t-dsp/t-dsp_tac5212_audio_shield_adaptor/3d_models/PinHeader_1x02_P2.54mm_Vertical.step

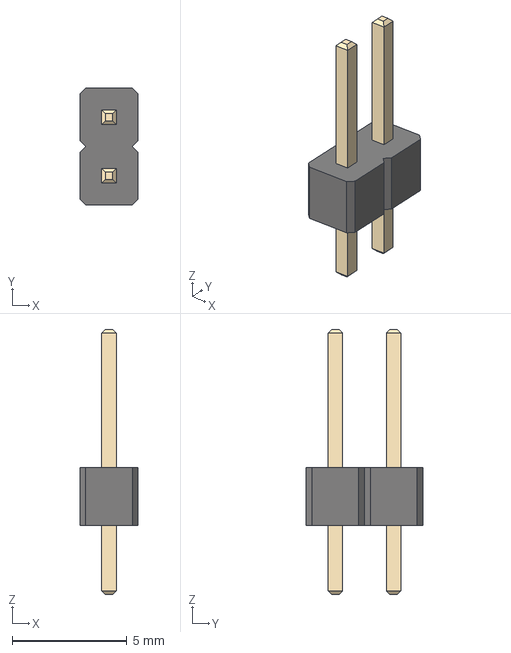
[picture p15: CAD file, 2026-03-01]
3d_models/PinHeader_1x02_P2.54mm_Vertical.step
2.54 x 5.08 x 11.5 mm
