t-dsp/t-dsp_tac5212_audio_shield_adaptor/3d_models/74LS00.step

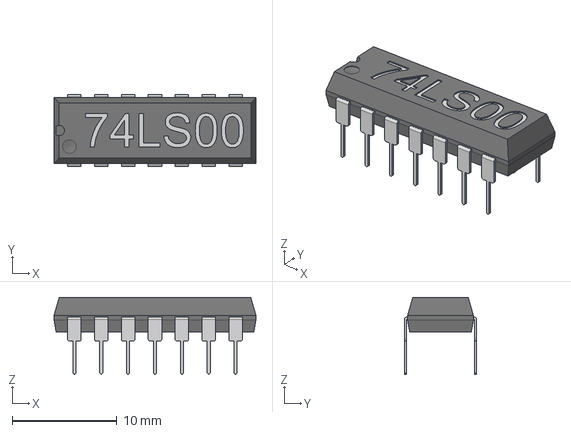
[picture p16: CAD file, 2026-03-01]
3d_models/74LS00.step
19.3 x 6.90 x 7.40 mm
