t-dsp/t-dsp_tac5212_audio_shield_adaptor/3d_models/d-nc3fah.stp

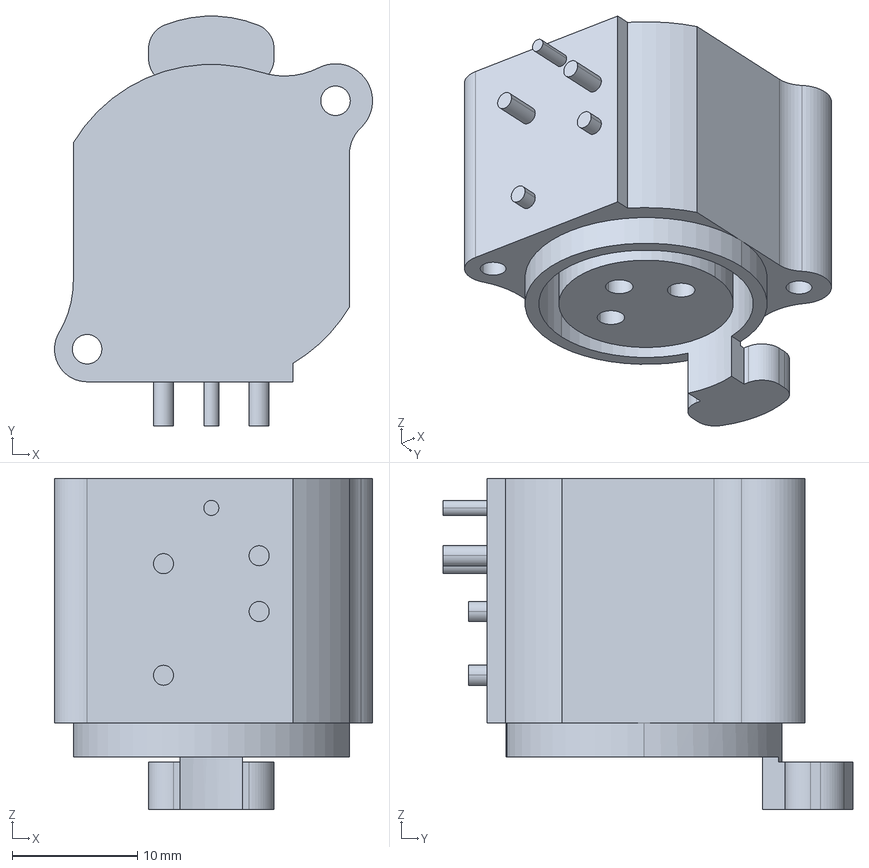
[picture p17: CAD file, 2026-03-01]
3d_models/d-nc3fah.stp
25.3 x 32.6 x 26.4 mm
