t-dsp/t-dsp_tac5212_audio_shield_adaptor/3d_models/COMBO_XLR_NCJ6FI-H-0.stp

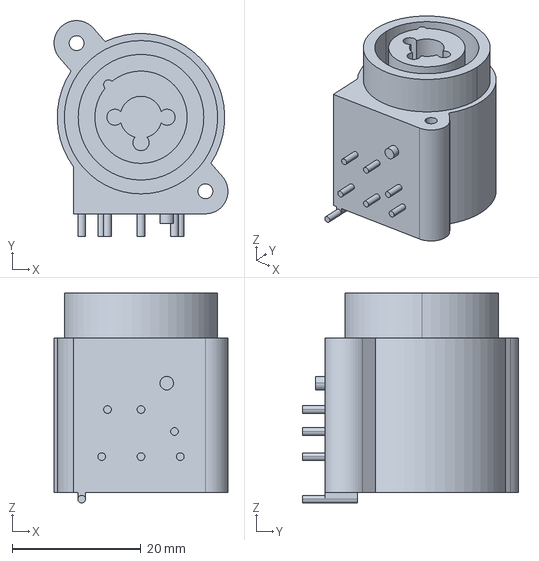
[picture p18: CAD file, 2026-03-01]
3d_models/COMBO_XLR_NCJ6FI-H-0.stp
27.0 x 33.5 x 32.6 mm
