t-dsp/t-dsp_tac5212_audio_shield_adaptor/3d_models/COMBO-NCJ6FA-H.step

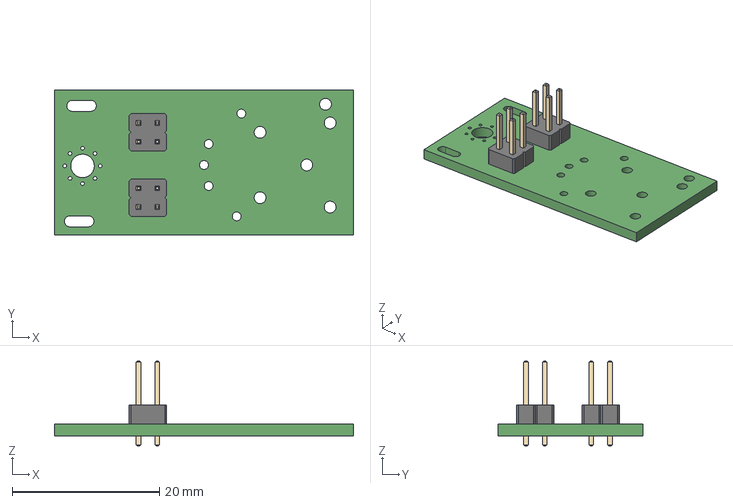
[picture p19: CAD file, 2026-03-01]
3d_models/COMBO-NCJ6FA-H.step
40.6 x 19.7 x 11.5 mm
