t-dsp/t-dsp_tac5212_audio_shield_adaptor/3d_models/35RAPC7JS_SIMPLIFIED.step

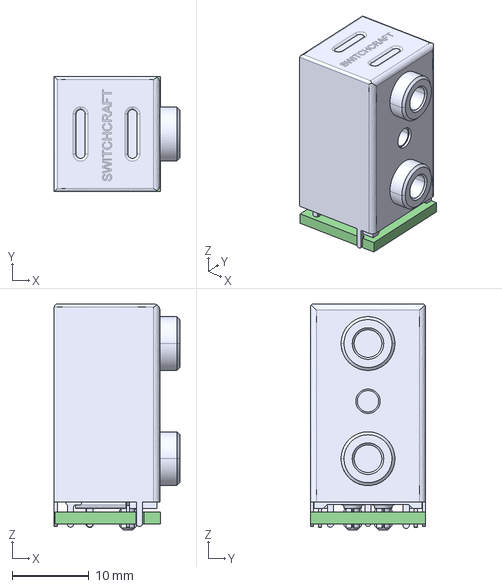
[picture p21: CAD file, 2026-03-01]
3d_models/35RAPC7JS_SIMPLIFIED.step
16.4 x 15.0 x 29.5 mm
IO_3.5_35RAPC7JS PCB
