t-dsp/t-dsp_tac5212_audio_shield_adaptor/3d_models/TFT_320x240_touch_r0.step

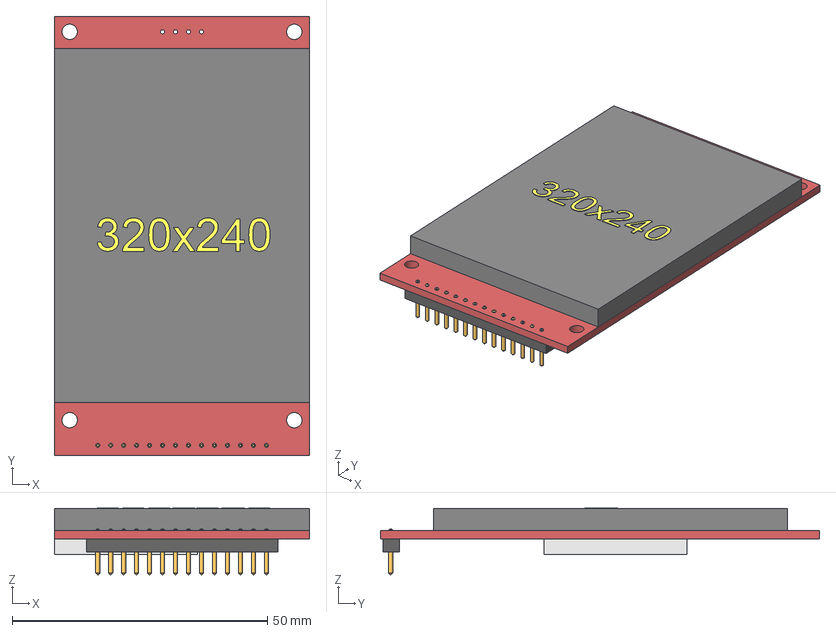
[picture p22: CAD file, 2026-03-01]
3d_models/TFT_320x240_touch_r0.step
50.0 x 86.0 x 13.1 mm
Body-header
Body-pins
Body-display
Body-sdcard
Body-board
