t-dsp/t-dsp_tac5212_audio_shield_adaptor/3d_models/pjras1x2s_Series.STEP

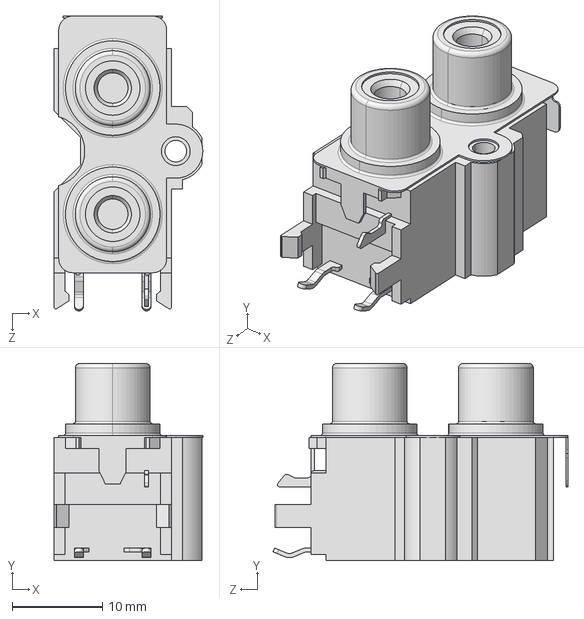
[picture p23: CAD file, 2026-03-01]
3d_models/pjras1x2s_Series.STEP
16.5 x 21.9 x 32.7 mm
