t-dsp/t-dsp_tac5212_audio_shield_adaptor/3d_models/H11L1SM.step

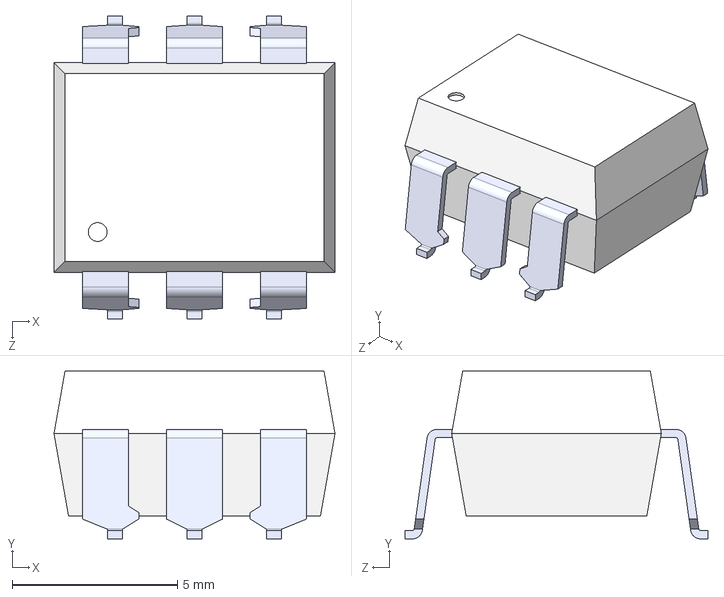
[picture p24: CAD file, 2026-03-01]
3d_models/H11L1SM.step
8.51 x 5.08 x 9.17 mm
