t-dsp/t-dsp_tac5212_audio_shield_adaptor/3d_models/MF-LSMF300_24X-2.stp

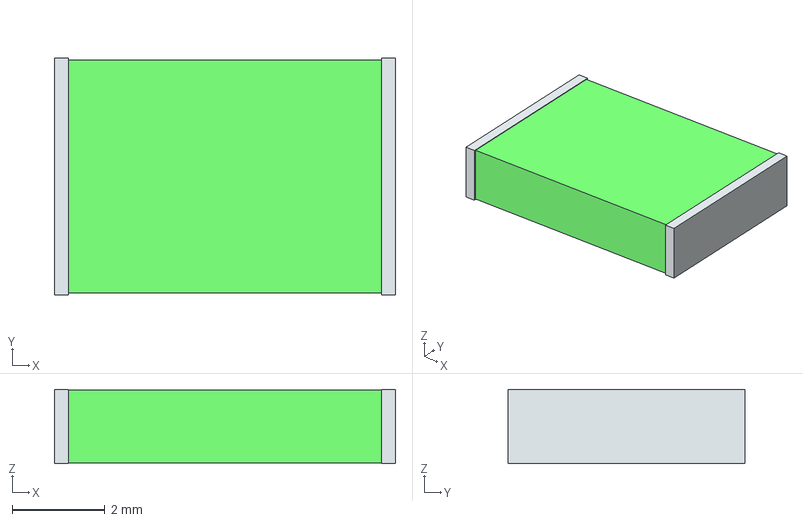
[picture p25: CAD file, 2026-03-01]
3d_models/MF-LSMF300_24X-2.stp
7.36 x 5.12 x 1.60 mm
term1
term2
