t-dsp/t-dsp_tac5212_audio_shield_adaptor/3d_models/EN11-HSM1AF15.STEP

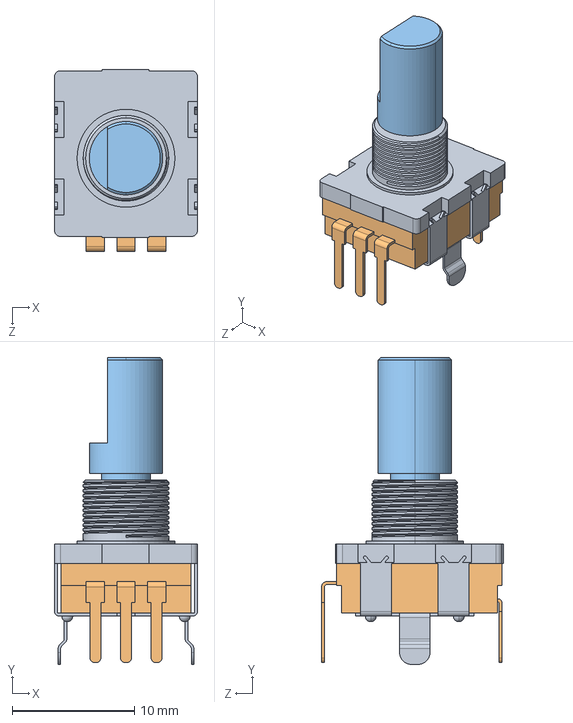
[picture p26: CAD file, 2026-03-01]
3d_models/EN11-HSM1AF15.STEP
11.7 x 25.1 x 14.9 mm
