t-dsp/t-dsp_tac5212_audio_shield_adaptor/3d_models/SD_CARD_DM3D-SF.step

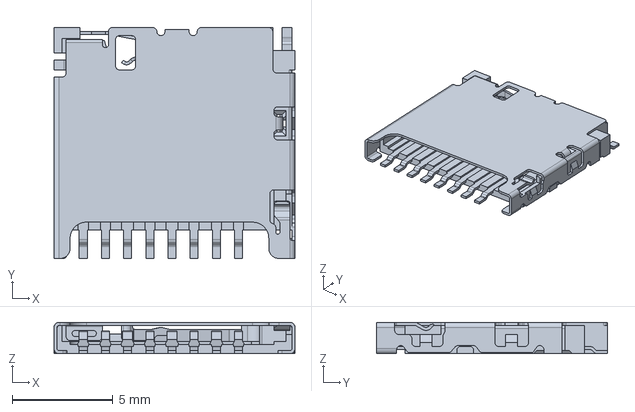
[picture p27: CAD file, 2026-03-01]
3d_models/SD_CARD_DM3D-SF.step
11.9 x 11.4 x 1.55 mm
