t-dsp/t-dsp_tac5212_audio_shield_adaptor/3d_models/SK6812.step

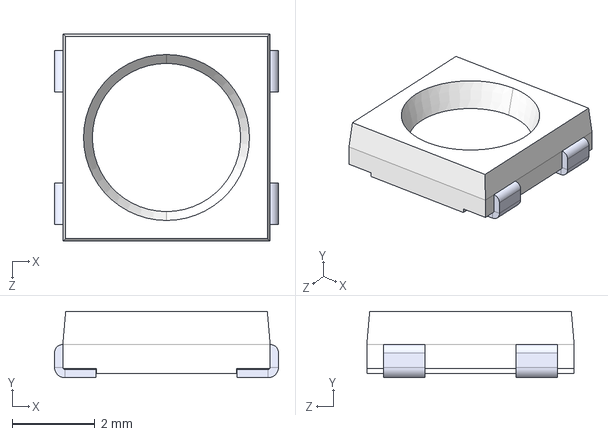
[picture p28: CAD file, 2026-03-01]
3d_models/SK6812.step
5.40 x 1.60 x 5.00 mm
