t-dsp/t-dsp_tac5212_audio_shield_adaptor/3d_models/c-292304-1-b-3d.stp

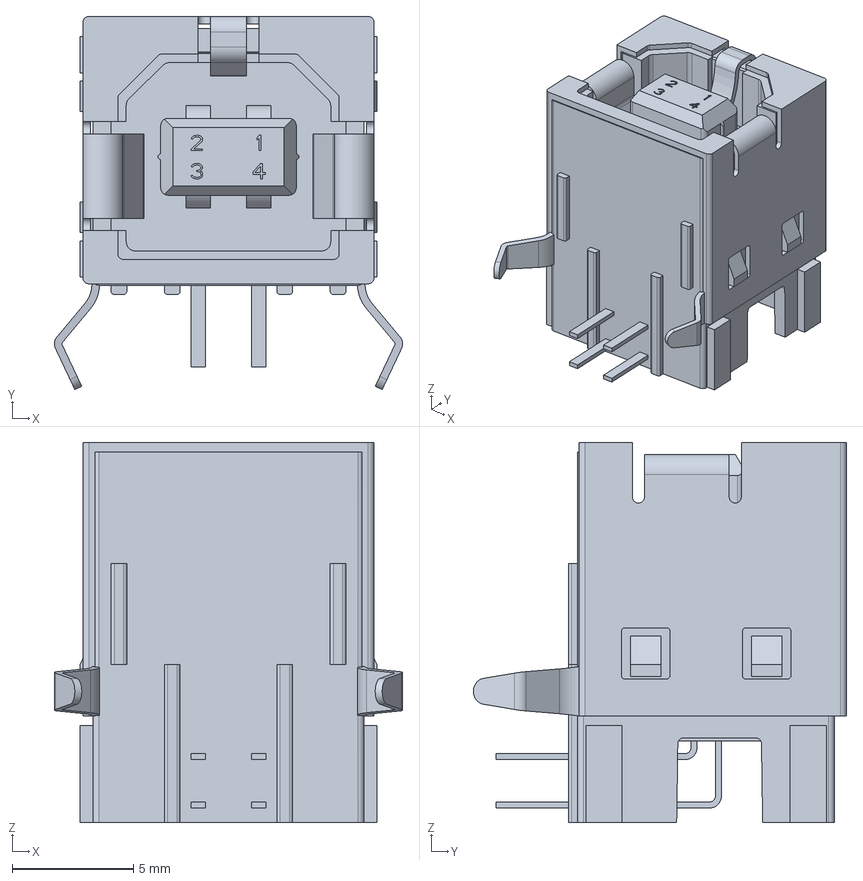
[picture p29: CAD file, 2026-03-01]
3d_models/c-292304-1-b-3d.stp
14.4 x 15.4 x 15.7 mm
