t-dsp/t-dsp_tac5212_audio_shield_adaptor/3d_models/T10W--3DModel-STEP-56544.STEP

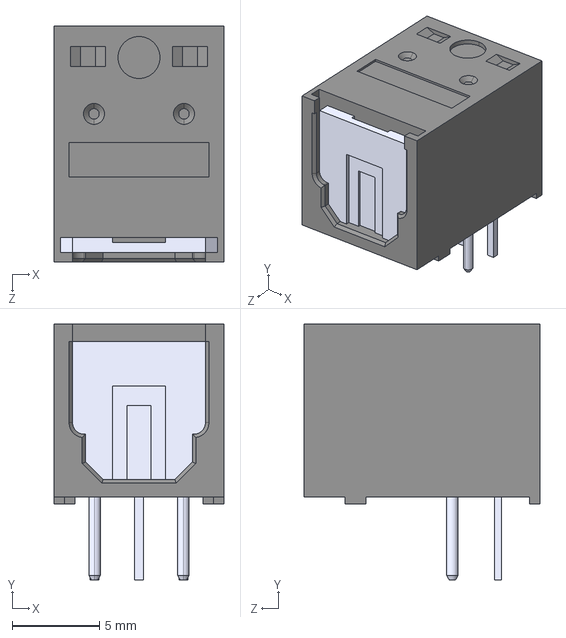
[picture p31: CAD file, 2026-03-01]
3d_models/T10W--3DModel-STEP-56544.STEP
9.70 x 14.7 x 13.5 mm
