t-dsp/t-dsp_tac5212_audio_shield_adaptor/3d_models/DIN-5.STEP

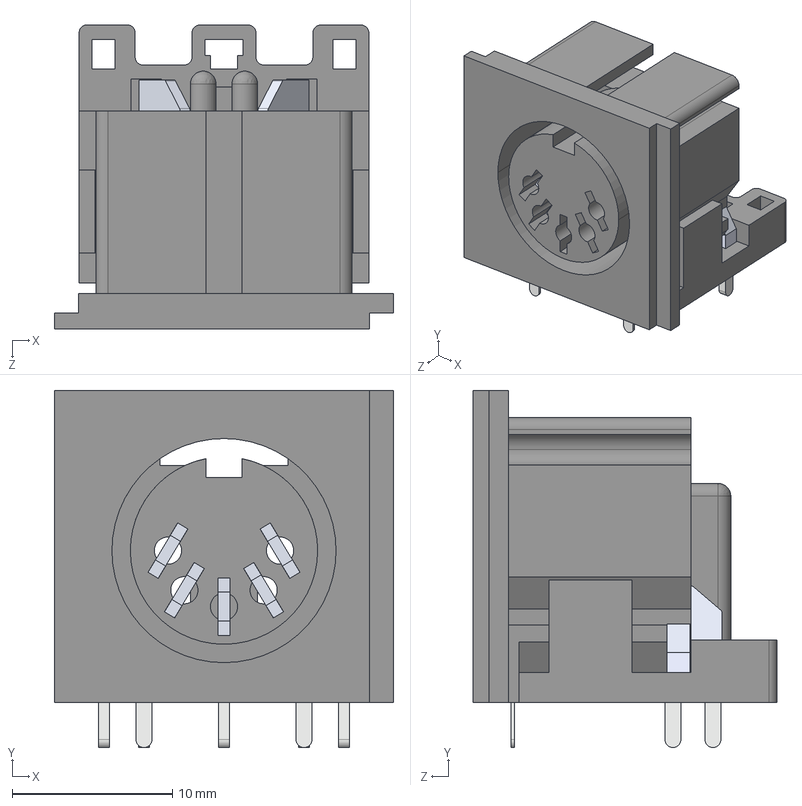
[picture p32: CAD file, 2026-03-01]
3d_models/DIN-5.STEP
21.2 x 22.3 x 19.0 mm
DIN5 A
DIN5 B
DIN5 C
DIN D x 2
DIN E x 2
DIN EE x 2
DIN G
DIN DD x 2
