t-dsp/t-dsp_tac5212_audio_shield_adaptor/3d_models/TOSLINK_3D_MODEL_PLT133_T9.step

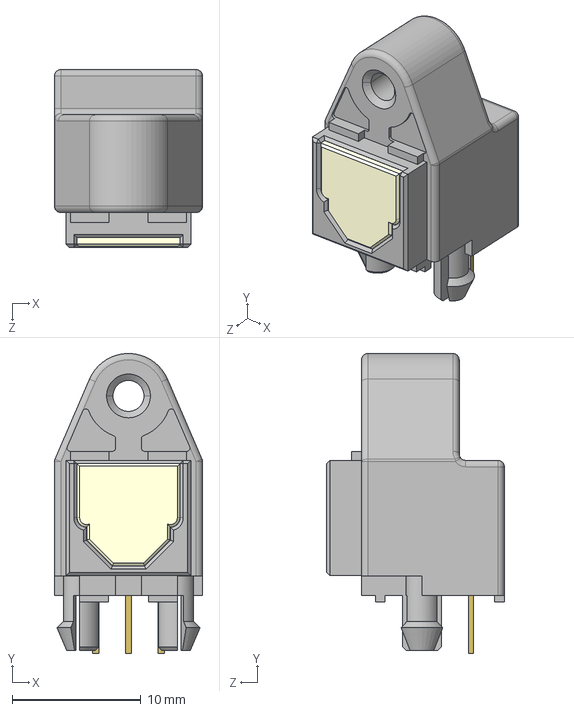
[picture p33: CAD file, 2026-03-01]
3d_models/TOSLINK_3D_MODEL_PLT133_T9.step
11.5 x 23.3 x 13.8 mm
