t-dsp/t-dsp_tac5212_audio_shield_adaptor/3d_models/Same_Sky_SJ3-35083D-TR.step

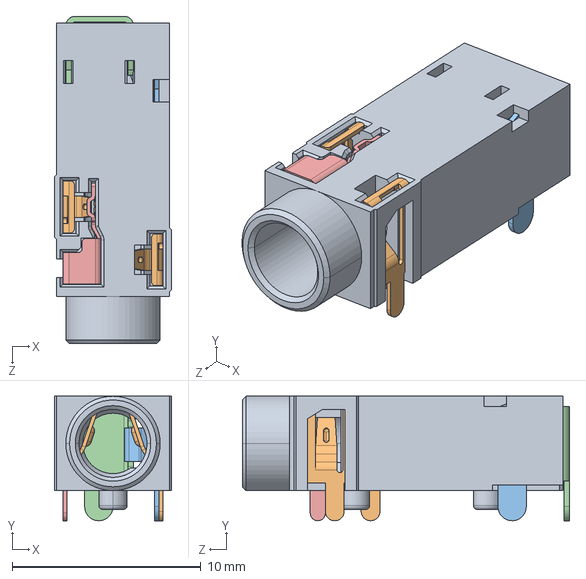
[picture p34: CAD file, 2026-03-01]
3d_models/Same_Sky_SJ3-35083D-TR.step
6.20 x 6.60 x 17.3 mm
