t-dsp/t-dsp_tac5212_audio_shield_adaptor/3d_models/2120--3DModel-STEP-630548.STEP

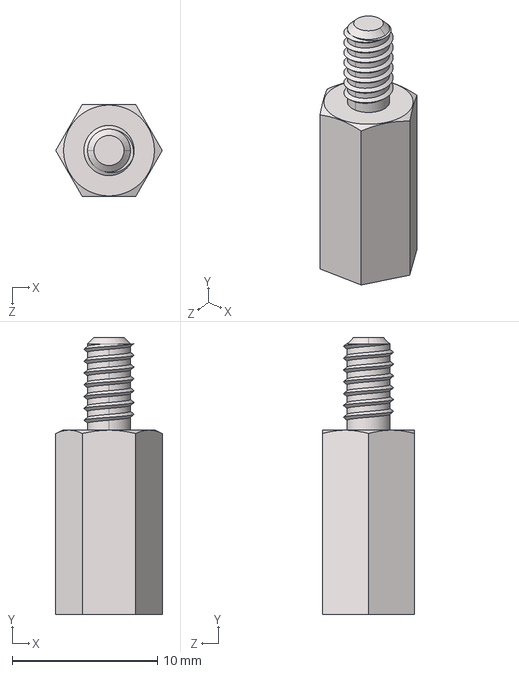
[picture p35: CAD file, 2026-03-01]
3d_models/2120--3DModel-STEP-630548.STEP
7.33 x 19.1 x 6.35 mm
