t-dsp/t-dsp_tac5212_audio_shield_adaptor/3d_models/3.5MM_STEREO_35RAPC4BHN2.STEP

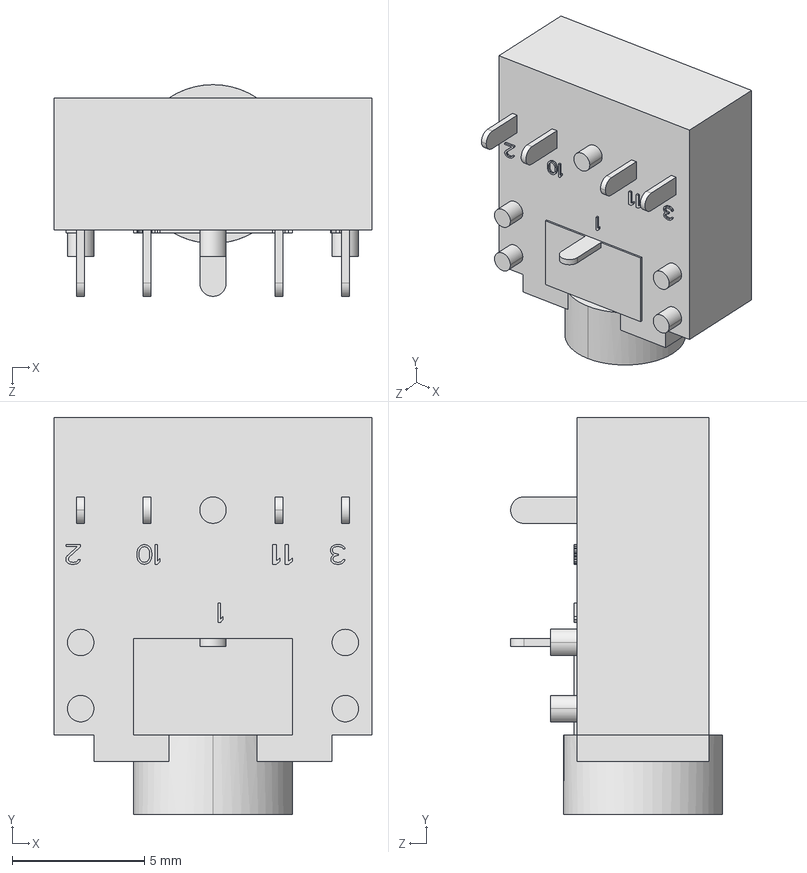
[picture p36: CAD file, 2026-03-01]
3d_models/3.5MM_STEREO_35RAPC4BHN2.STEP
12.0 x 15.0 x 8.00 mm
