t-dsp/t-dsp_tac5212_audio_shield_adaptor/3d_models/SPDIF_pjran1x1_Series.STEP

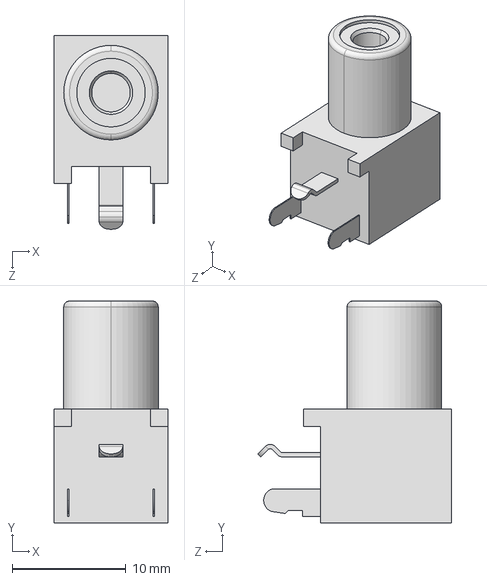
[picture p37: CAD file, 2026-03-01]
3d_models/SPDIF_pjran1x1_Series.STEP
10.00 x 19.5 x 17.0 mm
