t-dsp/t-dsp_tac5212_audio_shield_adaptor/3d_models/LED_SK6812MINI-E.step

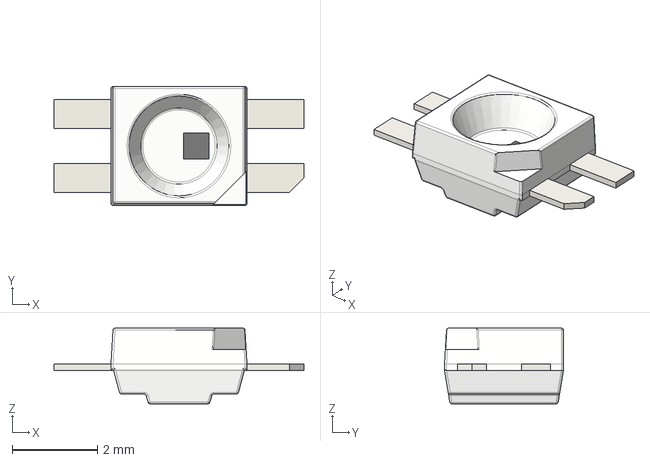
[picture p38: CAD file, 2026-03-01]
3d_models/LED_SK6812MINI-E.step
5.88 x 2.80 x 1.78 mm
