t-dsp/t-dsp_tac5212_audio_shield_adaptor/3d_models/USB-B1HS - USB-B1H Interconnect USB Type B.stp

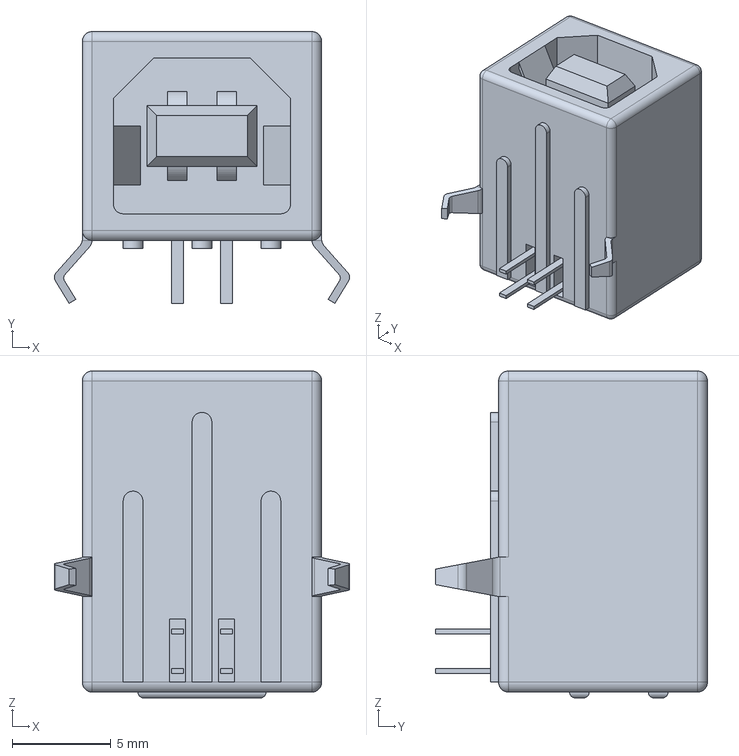
[picture p39: CAD file, 2026-03-01]
3d_models/USB-B1HS - USB-B1H Interconnect USB Type B.stp
15.0 x 13.8 x 16.6 mm
