t-dsp/t-dsp_tac5212_audio_shield_adaptor/3d_models/CP_Radial_D10.0mm_P5.00mm.step

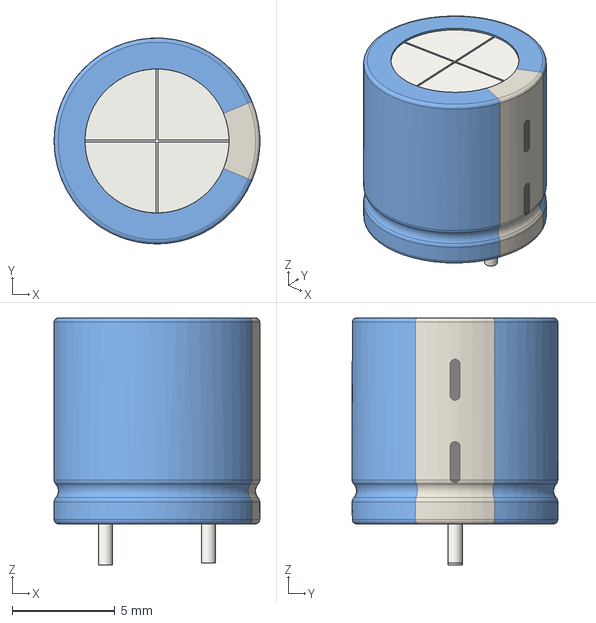
[picture p40: CAD file, 2026-03-01]
3d_models/CP_Radial_D10.0mm_P5.00mm.step
10.00 x 9.99 x 12.0 mm
