t-dsp/t-dsp_tac5212_audio_shield_adaptor/3d_models/SPK0641HT4H-1.step

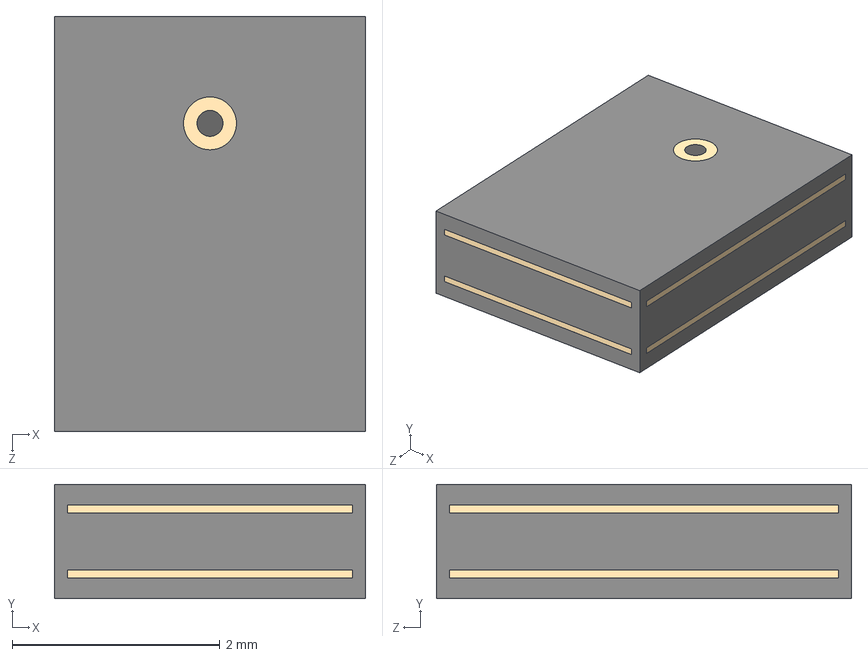
[picture p41: CAD file, 2026-03-01]
3d_models/SPK0641HT4H-1.step
3.00 x 1.10 x 4.00 mm
