t-dsp/t-dsp_tac5212_audio_shield_adaptor/3d_models/DMG2307L-7.stp

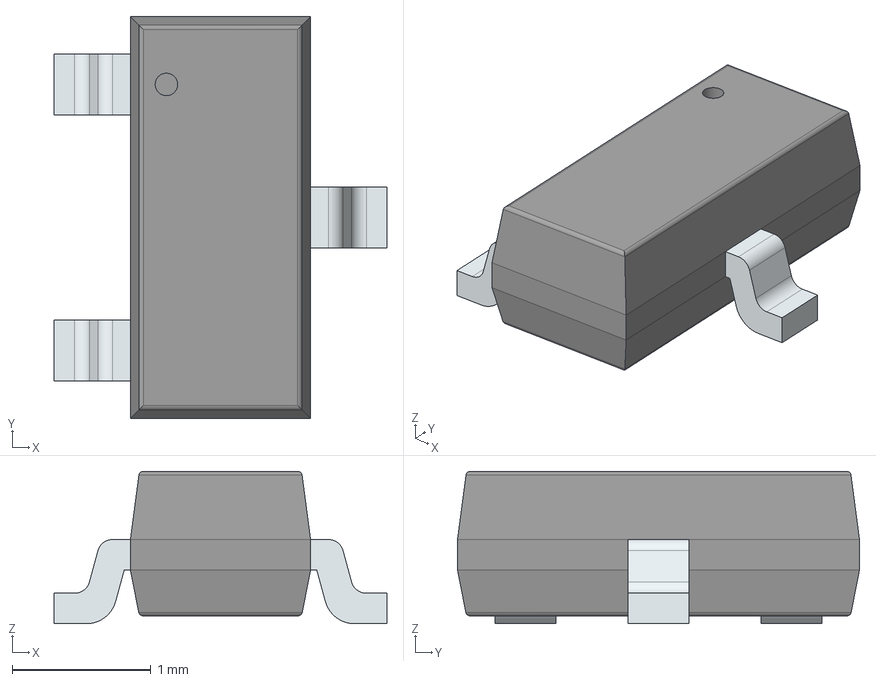
[picture p42: CAD file, 2026-03-01]
3d_models/DMG2307L-7.stp
2.40 x 2.90 x 1.10 mm
PinsArrayL
FilletPinR
