t-dsp/t-dsp_tac5212_audio_shield_adaptor/3d_models/SN74LVC1G66DBVR.stp

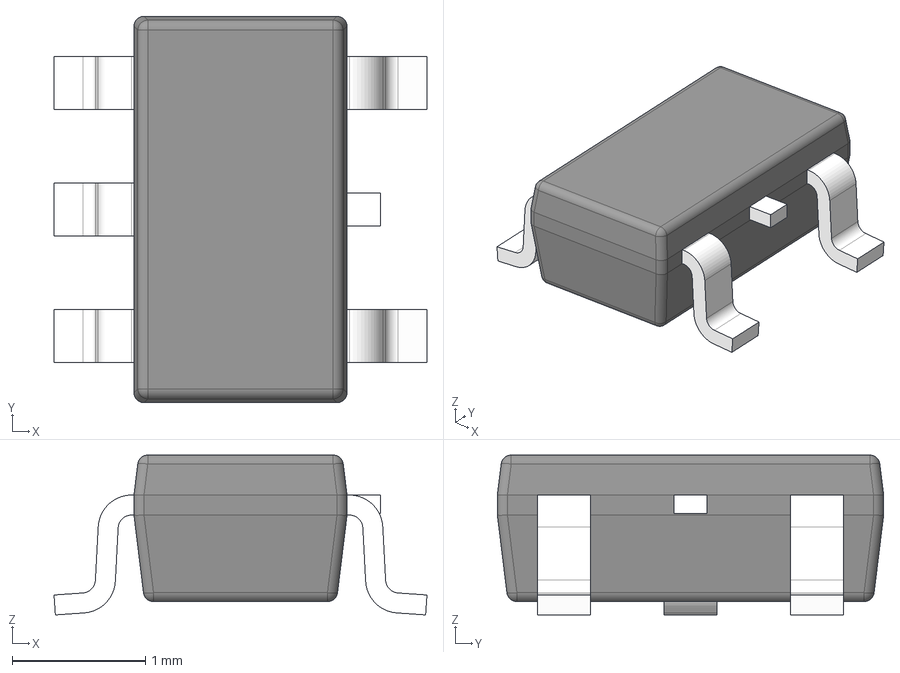
[picture p43: CAD file, 2026-03-01]
3d_models/SN74LVC1G66DBVR.stp
2.80 x 2.90 x 1.20 mm
BODY-SOT
LEAD-SOT x 5
LEAD-DUMMY
