t-dsp/t-dsp_tac5212_audio_shield_adaptor/3d_models/SOT-23-6.step

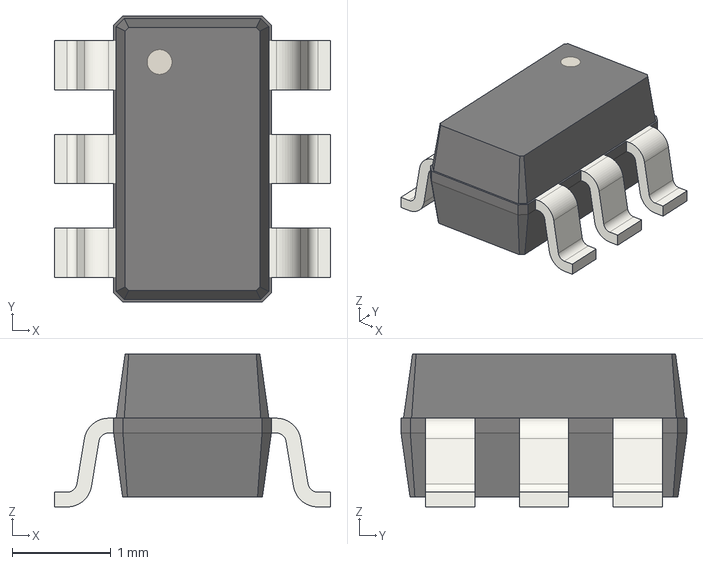
[picture p44: CAD file, 2026-03-01]
3d_models/SOT-23-6.step
2.80 x 2.90 x 1.55 mm
