t-dsp/t-dsp_tac5212_audio_shield_adaptor/3d_models/USB_A_c-292303-4-f-3d.stp

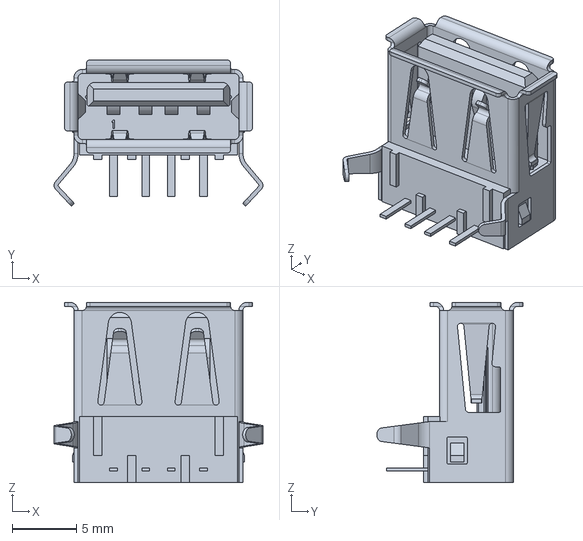
[picture p46: CAD file, 2026-03-01]
3d_models/USB_A_c-292303-4-f-3d.stp
16.2 x 11.4 x 14.0 mm
