t-dsp/t-dsp_tac5212_audio_shield_adaptor/3d_models/D_1210_3225Metric.step

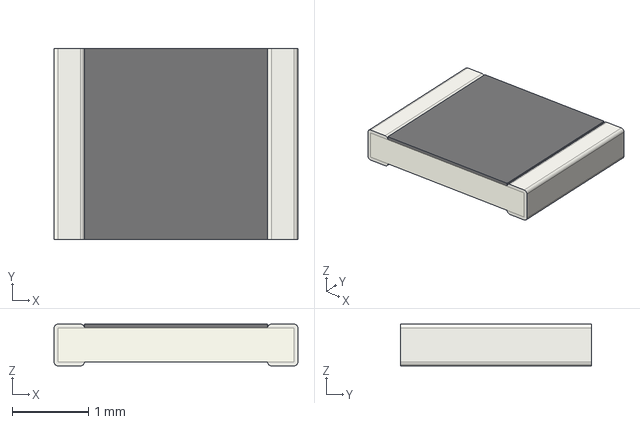
[picture p47: CAD file, 2026-03-01]
3d_models/D_1210_3225Metric.step
3.20 x 2.50 x 0.55 mm
