t-dsp/t-dsp_tac5212_audio_shield_adaptor/3d_models/IDC-Header_2x10_P2.54mm_Vertical.step

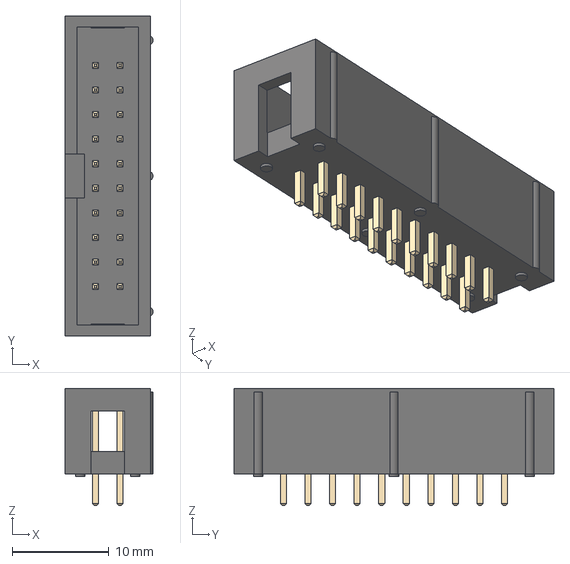
[picture p48: CAD file, 2026-03-01]
3d_models/IDC-Header_2x10_P2.54mm_Vertical.step
9.10 x 33.1 x 12.1 mm
