t-dsp/t-dsp_tac5212_audio_shield_adaptor/3d_models/ncj6fav-1.stp

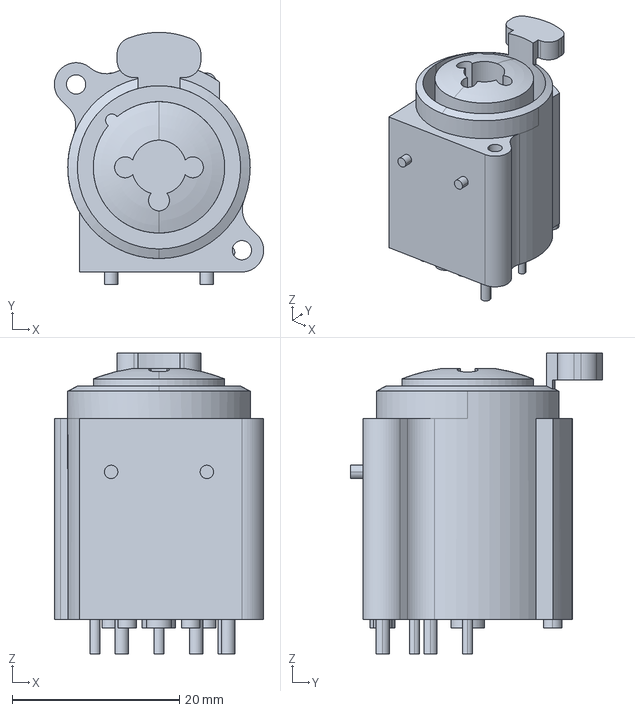
[picture p50: CAD file, 2026-03-01]
3d_models/ncj6fav-1.stp
25.0 x 30.1 x 36.0 mm
