t-dsp/t-dsp_tac5212_audio_shield_adaptor/3d_models/LED_D5.0mm_Clear.step

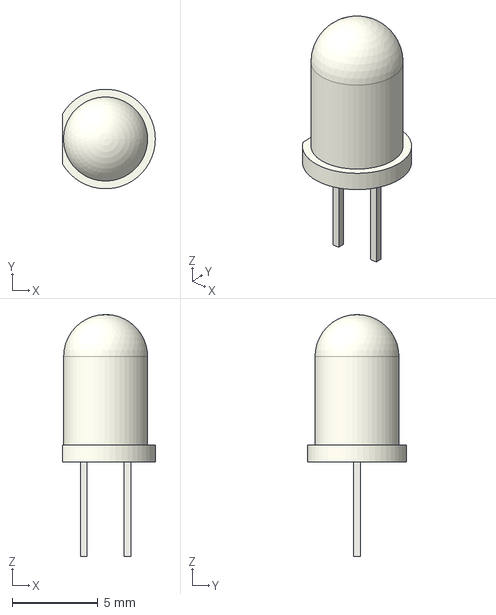
[picture p51: CAD file, 2026-03-01]
3d_models/LED_D5.0mm_Clear.step
5.40 x 5.79 x 14.1 mm
