t-dsp/t-dsp_tac5212_audio_shield_adaptor/3d_models/SOT-583-8.step

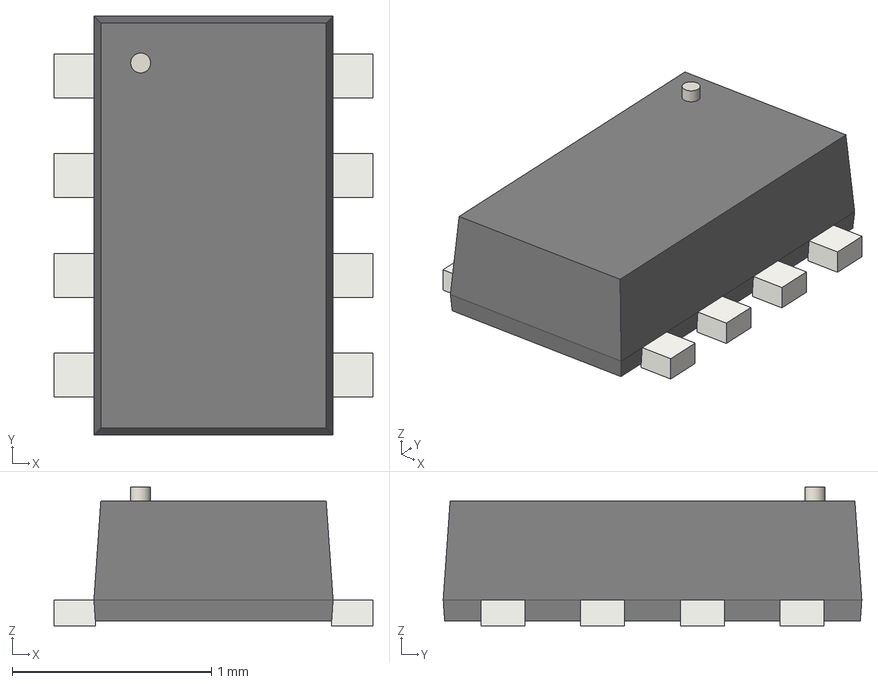
[picture p52: CAD file, 2026-03-01]
3d_models/SOT-583-8.step
1.60 x 2.10 x 0.695 mm
