t-dsp/t-dsp_tac5212_audio_shield_adaptor/3d_models/SOIC-14_3.9x8.7mm_P1.27mm.step

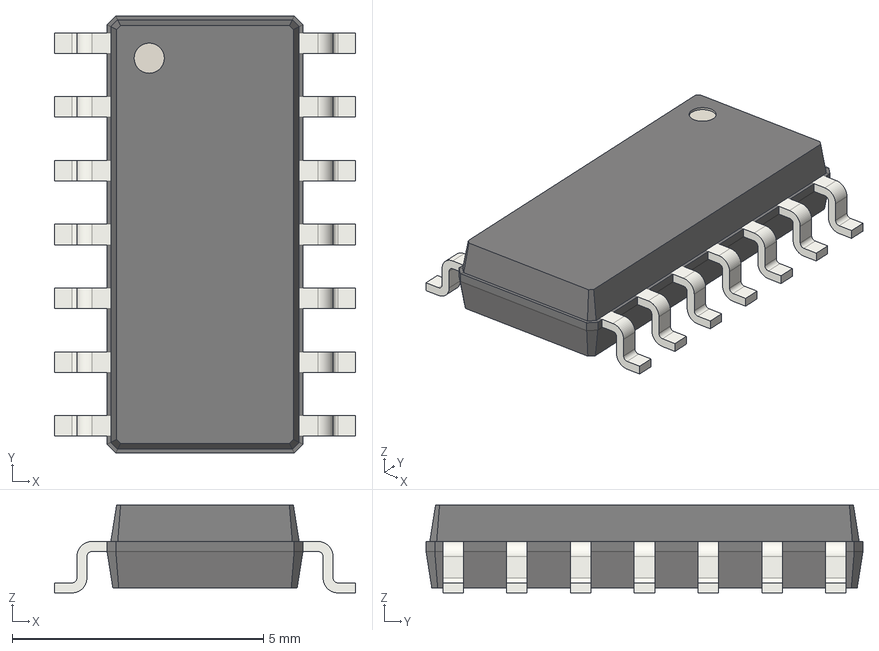
[picture p53: CAD file, 2026-03-01]
3d_models/SOIC-14_3.9x8.7mm_P1.27mm.step
6.00 x 8.70 x 1.75 mm
