t-dsp/t-dsp_tac5212_audio_shield_adaptor/3d_models/SN74LVC2G125DCTR.step

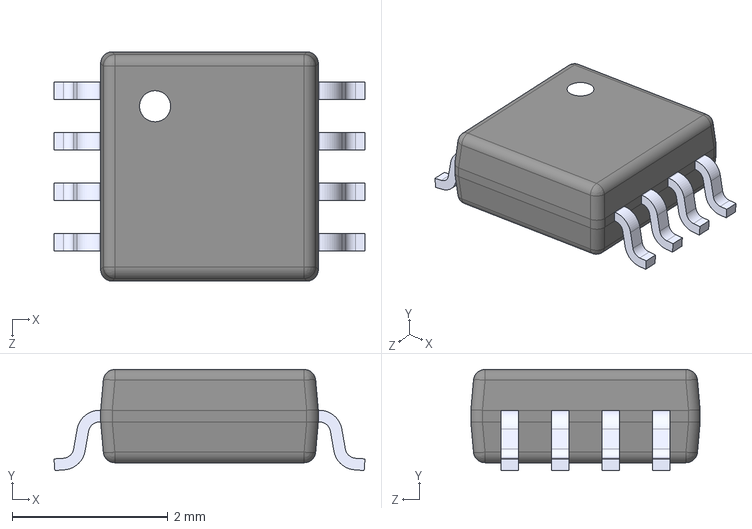
[picture p55: CAD file, 2026-03-01]
3d_models/SN74LVC2G125DCTR.step
4.00 x 1.30 x 2.95 mm
