t-dsp/t-dsp_tac5212_audio_shield_adaptor/3d_models/SOIC-14W_7.5x9.0mm_P1.27mm.step

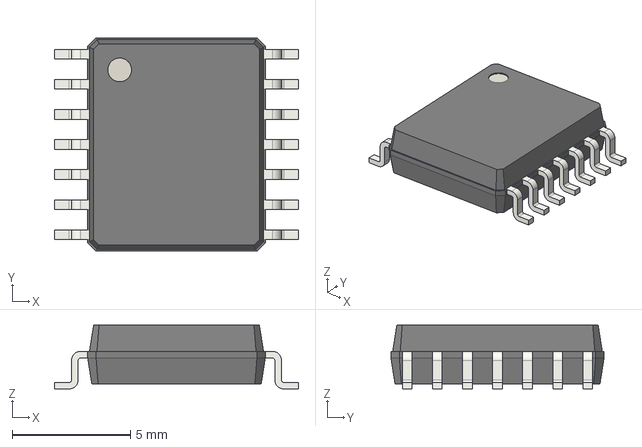
[picture p56: CAD file, 2026-03-01]
3d_models/SOIC-14W_7.5x9.0mm_P1.27mm.step
10.3 x 9.00 x 2.70 mm
