t-dsp/t-dsp_tac5212_audio_shield_adaptor/3d_models/JST_XH_S2B-XH-A_1x02_P2.50mm_Horizontal.step

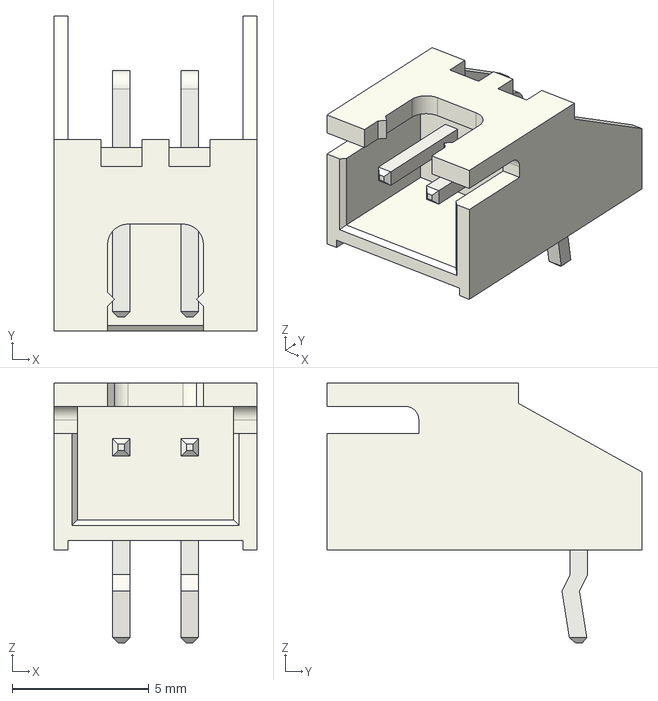
[picture p57: CAD file, 2026-03-01]
3d_models/JST_XH_S2B-XH-A_1x02_P2.50mm_Horizontal.step
7.40 x 11.5 x 9.50 mm
