t-dsp/t-dsp_tac5212_audio_shield_adaptor/3d_models/pjras2x2s_Series.STEP

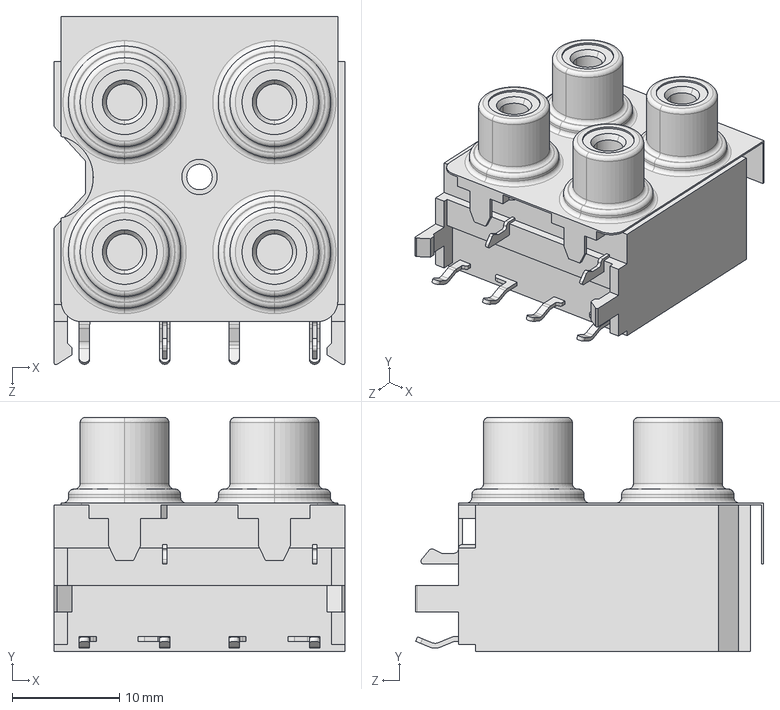
[picture p58: CAD file, 2026-03-01]
3d_models/pjras2x2s_Series.STEP
27.2 x 21.9 x 32.5 mm
