t-dsp/t-dsp_tac5212_audio_shield_adaptor/3d_models/C_1206_3216Metric.step

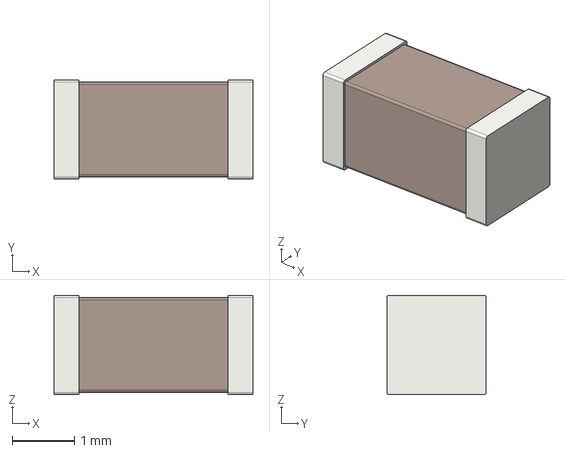
[picture p61: CAD file, 2026-03-01]
3d_models/C_1206_3216Metric.step
3.20 x 1.60 x 1.60 mm
