t-dsp/t-dsp_tac5212_audio_shield_adaptor/3d_models/PinSocket_1x08_P2.54mm_Vertical.step

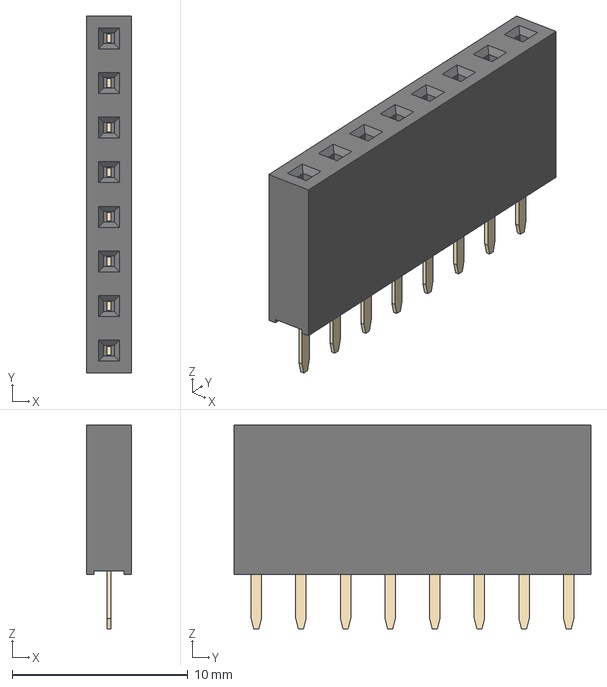
[picture p62: CAD file, 2026-03-01]
3d_models/PinSocket_1x08_P2.54mm_Vertical.step
2.54 x 20.3 x 11.6 mm
