t-dsp/t-dsp_tac5212_audio_shield_adaptor/3d_models/PEC12R-2220F-S0024.step

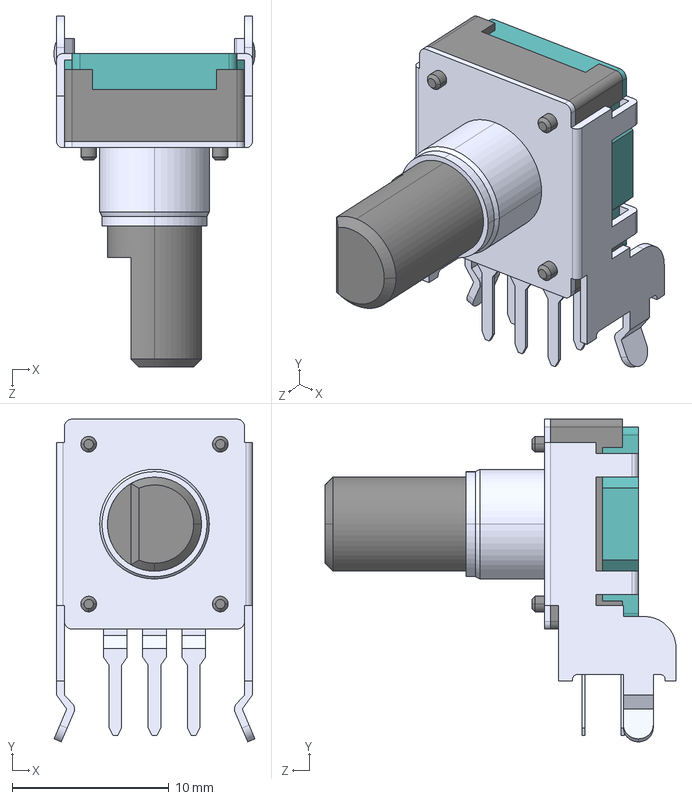
[picture p63: CAD file, 2026-03-01]
3d_models/PEC12R-2220F-S0024.step
12.8 x 20.6 x 22.4 mm
