t-dsp/t-dsp_tac5212_audio_shield_adaptor/3d_models/PinHeader_1x01_P2.54mm_Vertical.step

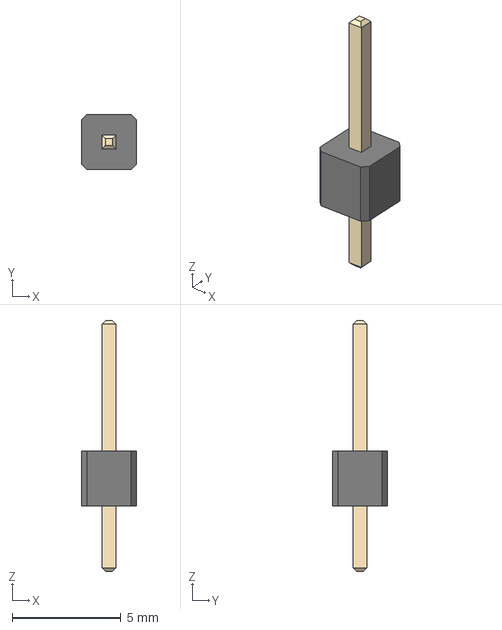
[picture p64: CAD file, 2026-03-01]
3d_models/PinHeader_1x01_P2.54mm_Vertical.step
2.54 x 2.54 x 11.5 mm
