t-dsp/t-dsp_tac5212_audio_shield_adaptor/3d_models/DC_BARREL_PJ-202AH.step

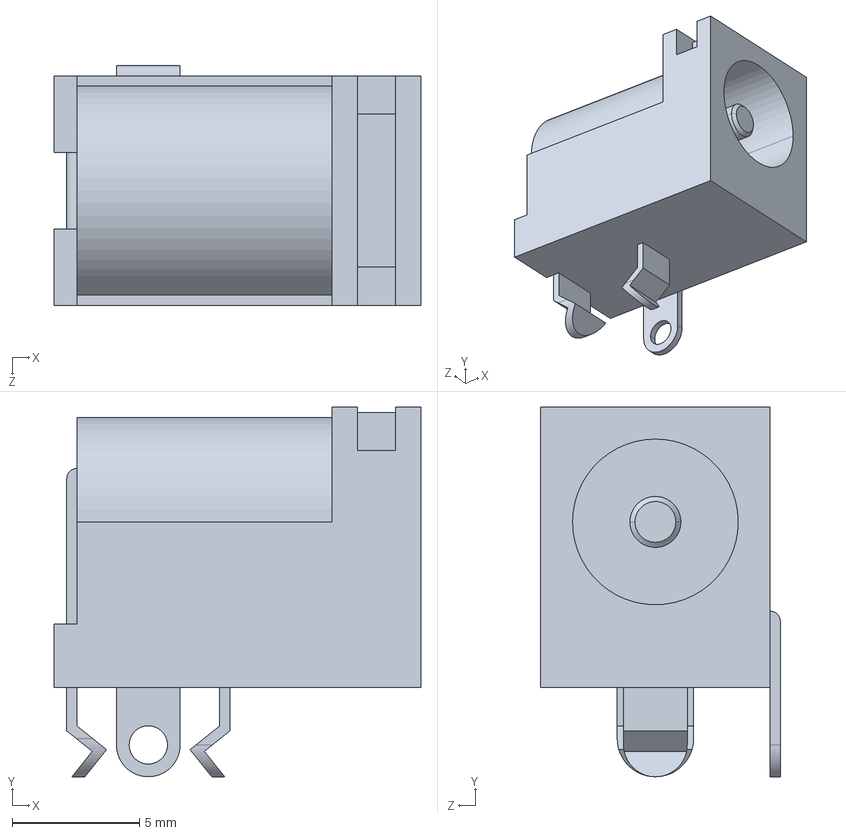
[picture p65: CAD file, 2026-03-01]
3d_models/DC_BARREL_PJ-202AH.step
14.4 x 14.5 x 9.40 mm
