t-dsp/t-dsp_tac5212_audio_shield_adaptor/3d_models/J1B1211CCD.STEP

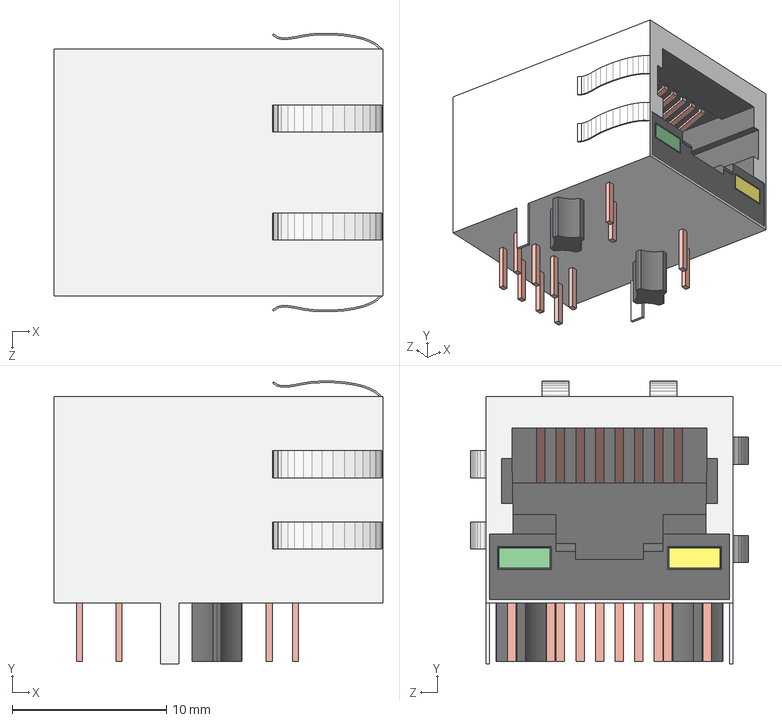
[picture p66: CAD file, 2026-03-01]
3d_models/J1B1211CCD.STEP
21.3 x 18.3 x 18.0 mm
