t-dsp/t-dsp_tac5212_audio_shield_adaptor/3d_models/TPD4E02B04DQA.step

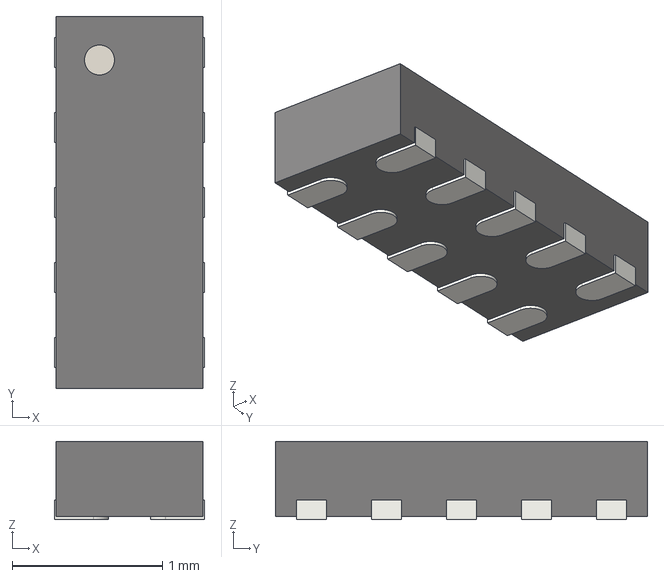
[picture p67: CAD file, 2026-03-01]
3d_models/TPD4E02B04DQA.step
1.00 x 2.48 x 0.52 mm
