t-dsp/t-dsp_tac5212_audio_shield_adaptor/3d_models/35RAPC3BH3.STEP

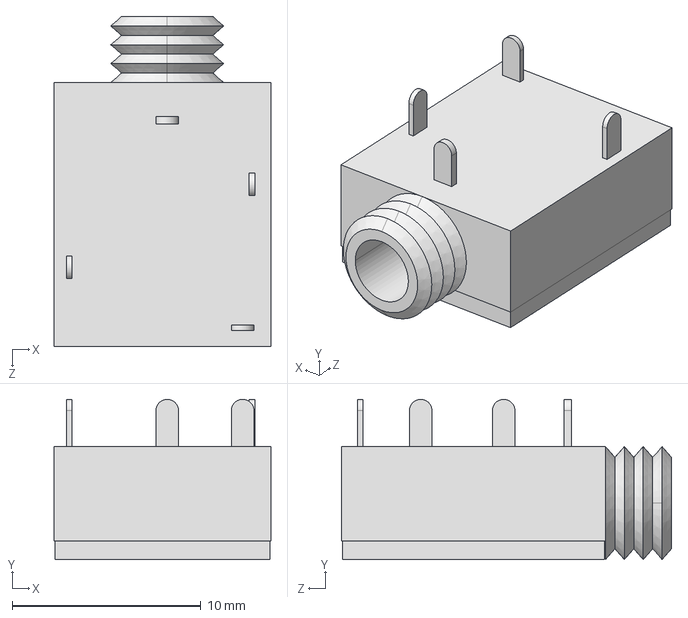
[picture p69: CAD file, 2026-03-01]
3d_models/35RAPC3BH3.STEP
11.5 x 8.50 x 17.5 mm
