t-dsp/t-dsp_tac5212_audio_shield_adaptor/3d_models/PinSocket_2x10_P2.54mm_Vertical.step

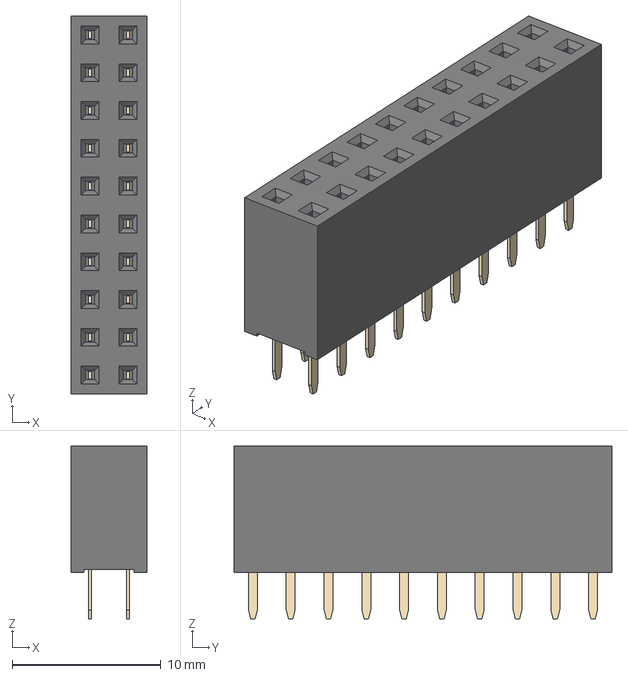
[picture p70: CAD file, 2026-03-01]
3d_models/PinSocket_2x10_P2.54mm_Vertical.step
5.08 x 25.4 x 11.6 mm
