t-dsp/t-dsp_tac5212_audio_shield_adaptor/3d_models/TPS2116DRLR.stp

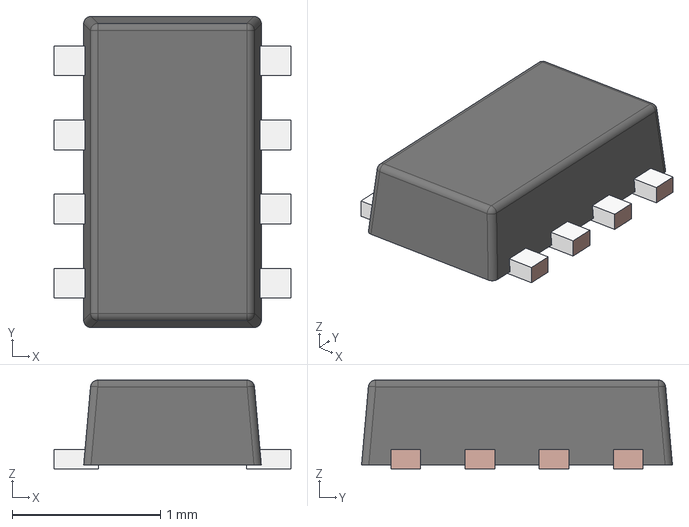
[picture p71: CAD file, 2026-03-01]
3d_models/TPS2116DRLR.stp
1.60 x 2.10 x 0.6 mm
FRAME-DRL0008A
BODY-SOT
