t-dsp/t-dsp_tac5212_audio_shield_adaptor/3d_models/JST - XH - Thru (V) - 2Pin - 2.54mm.stp

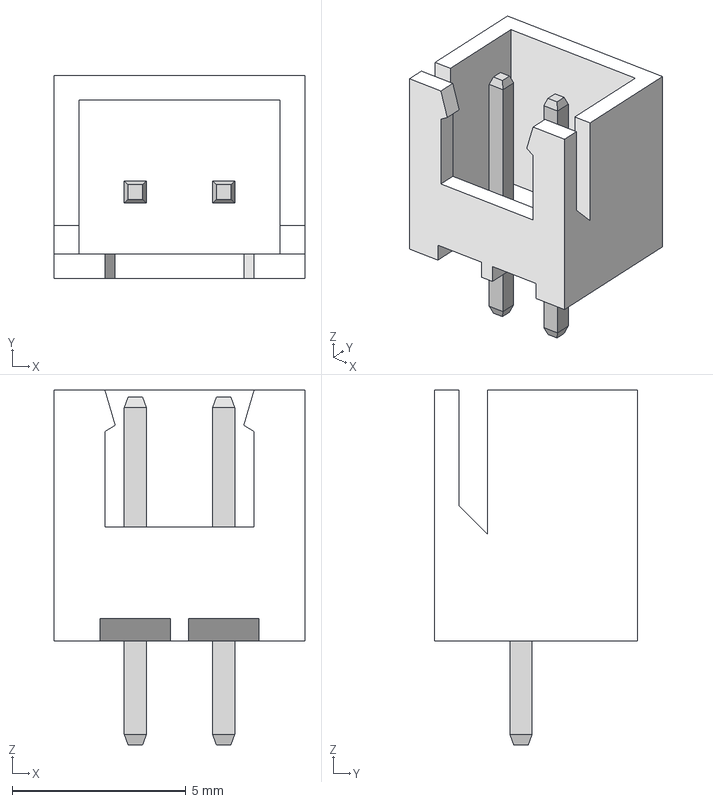
[picture p72: CAD file, 2026-03-01]
3d_models/JST - XH - Thru (V) - 2Pin - 2.54mm.stp
7.21 x 5.84 x 10.2 mm
