t-dsp/t-dsp_tac5212_audio_shield_adaptor/3d_models/1808--3DModel-STEP-630548.STEP

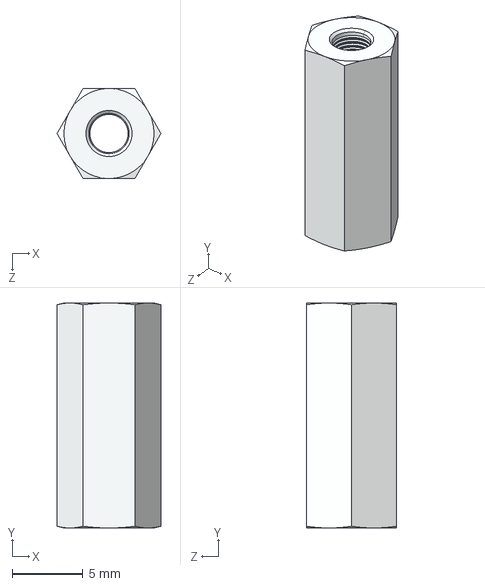
[picture p73: CAD file, 2026-03-01]
3d_models/1808--3DModel-STEP-630548.STEP
7.33 x 15.9 x 6.35 mm
