t-dsp/t-dsp_tac5212_audio_shield_adaptor/3d_models/TPD1E10B06DPYT.stp

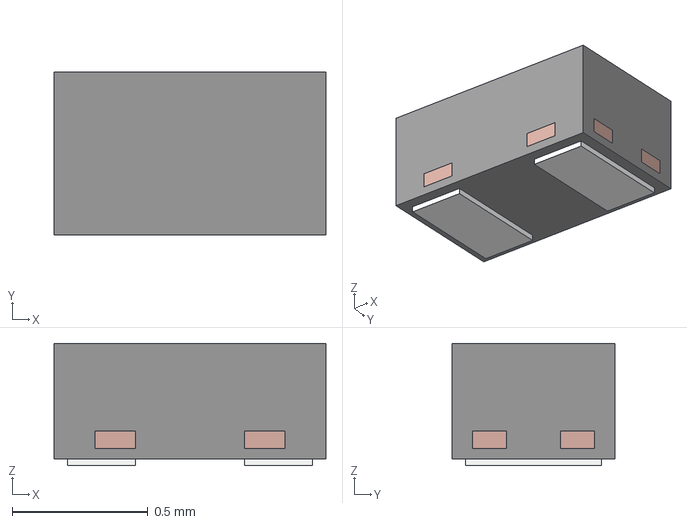
[picture p74: CAD file, 2026-03-01]
3d_models/TPD1E10B06DPYT.stp
1.00 x 0.6 x 0.45 mm
BODY-SON
FRAME-DPY0002A
