t-dsp/t-dsp_tac5212_audio_shield_adaptor/3d_models/3-D NCJ6FAH.stp

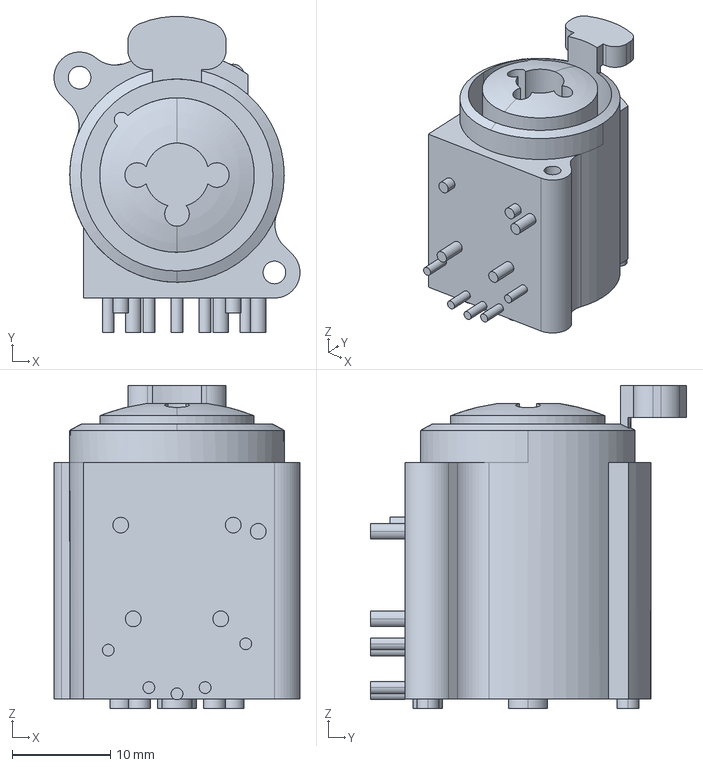
[picture p75: CAD file, 2026-03-01]
3d_models/3-D NCJ6FAH.stp
25.0 x 32.1 x 32.9 mm
