t-dsp/t-dsp_tac5212_audio_shield_adaptor/3d_models/PinSocket_1x02_P2.54mm_Vertical.step

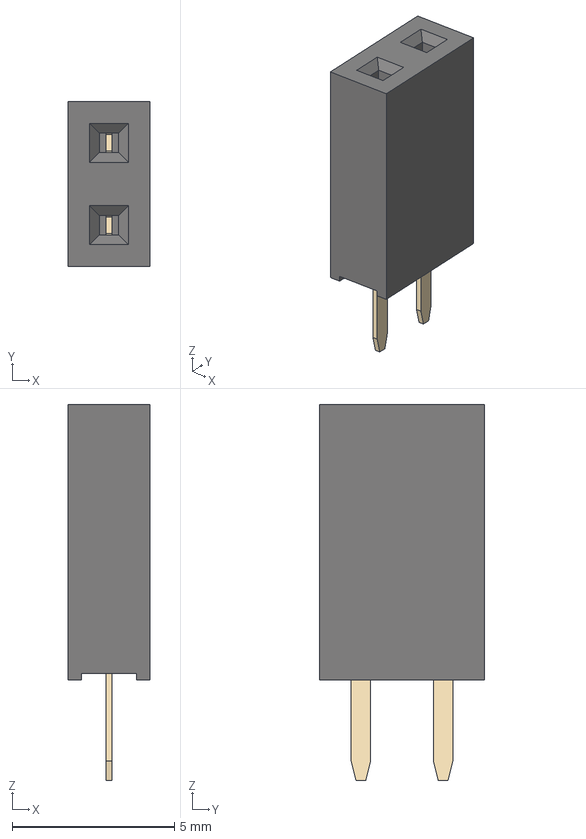
[picture p76: CAD file, 2026-03-01]
3d_models/PinSocket_1x02_P2.54mm_Vertical.step
2.54 x 5.08 x 11.6 mm
