t-dsp/t-dsp_tac5212_audio_shield_adaptor/3d_models/Tactile_Switch_4.54.5MM.stp

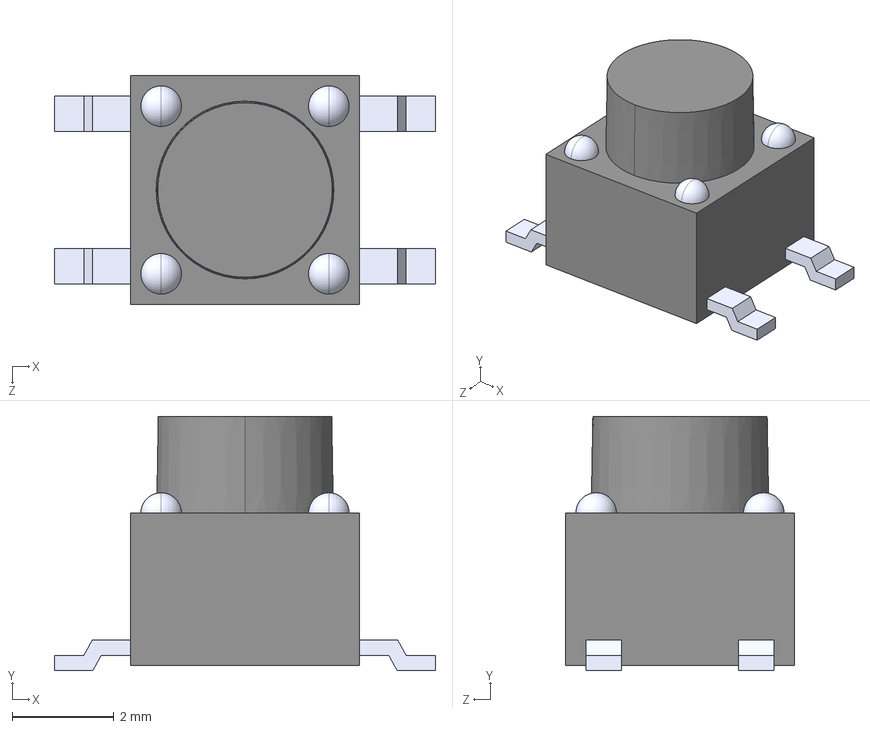
[picture p77: CAD file, 2026-03-01]
3d_models/Tactile_Switch_4.54.5MM.stp
7.50 x 5.00 x 4.50 mm
