t-dsp/t-dsp_tac5212_audio_shield_adaptor/3d_models/PJRAS2X1S01X.step

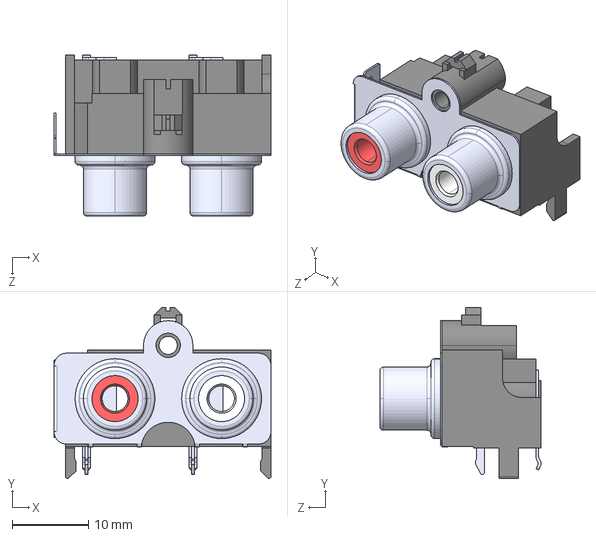
[picture p78: CAD file, 2026-03-01]
3d_models/PJRAS2X1S01X.step
28.5 x 22.5 x 21.2 mm
