t-dsp/t-dsp_tac5212_audio_shield_adaptor/3d_models/35RAPC7JS.STEP

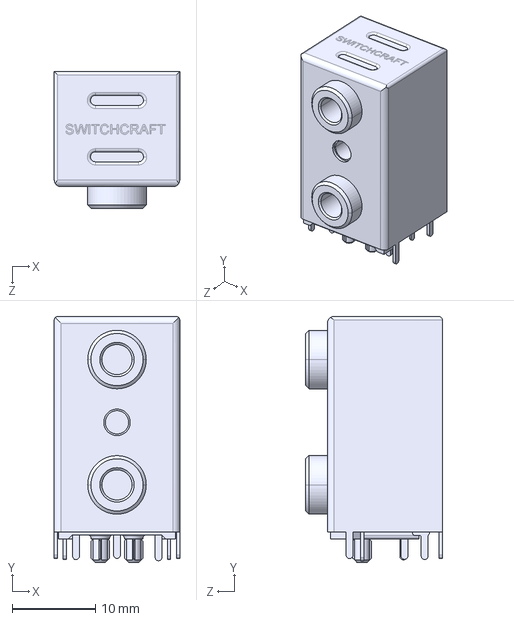
[picture p79: CAD file, 2026-03-01]
3d_models/35RAPC7JS.STEP
15.0 x 29.5 x 16.4 mm
