t-dsp/t-dsp_tac5212_audio_shield_adaptor/3d_models/t-dsp_tac5212_pro_audio_module_pcb_mount.step

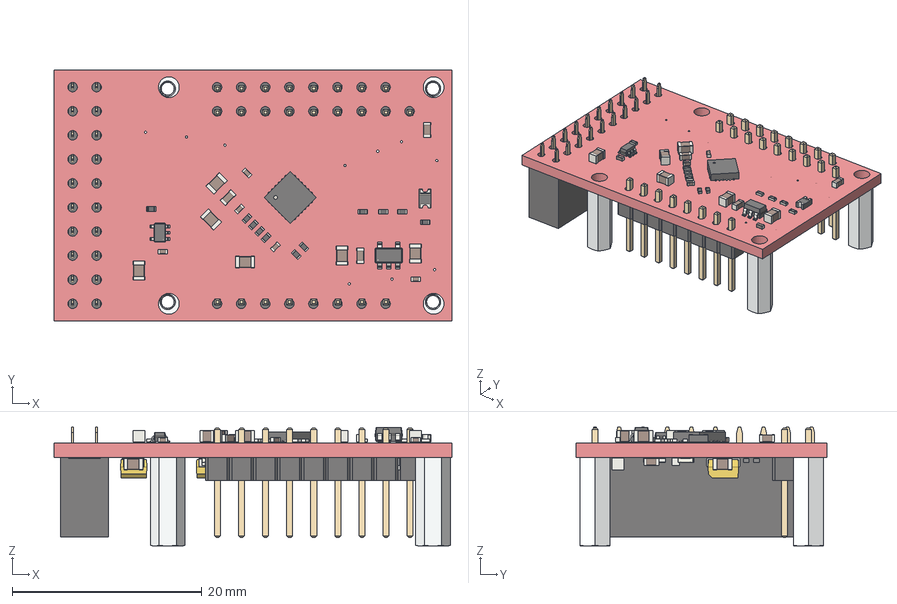
[picture p80: CAD file, 2026-03-01]
3d_models/t-dsp_tac5212_pro_audio_module_pcb_mount.step
42.0 x 26.5 x 12.5 mm
R_0402_1005Metric x 11
1808--3DModel-STEP-630548 x 4
PinHeader_1x08_P2.54mm_Vertical x 2
PinHeader_1x09_P2.54mm_Vertical
PinSocket_2x10_P2.54mm_Vertical
C_0805_2012Metric x 11
C_0402_1005Metric x 5
C_0603_1608Metric x 11
SOT-353_SC-70-5
SOT-23-5
D_0805_2012Metric
VQFN-24-1EP_4x4mm_P0.5mm_EP2.45x2.45mm
R_0603_1608Metric x 16
CP_EIA-3528-21_Kemet-B x 4
TPD1E10B06DPYR x 8
t-dsp_tac5212_pro_audio_module_PCB
