t-dsp/t-dsp_tac5212_audio_shield_adaptor/3d_models/Same_Sky_SJ3-35044A.step

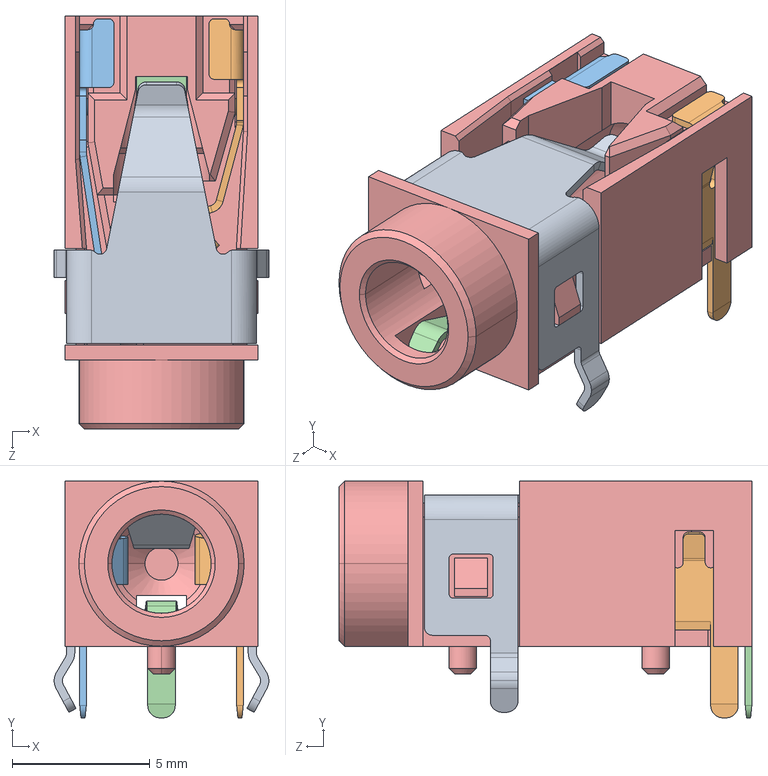
[picture p82: CAD file, 2026-03-01]
3d_models/Same_Sky_SJ3-35044A.step
7.80 x 8.60 x 15.0 mm
