t-dsp/t-dsp_tac5212_audio_shield_adaptor/3d_models/PinHeader_2x03_P2.54mm_Horizontal.step

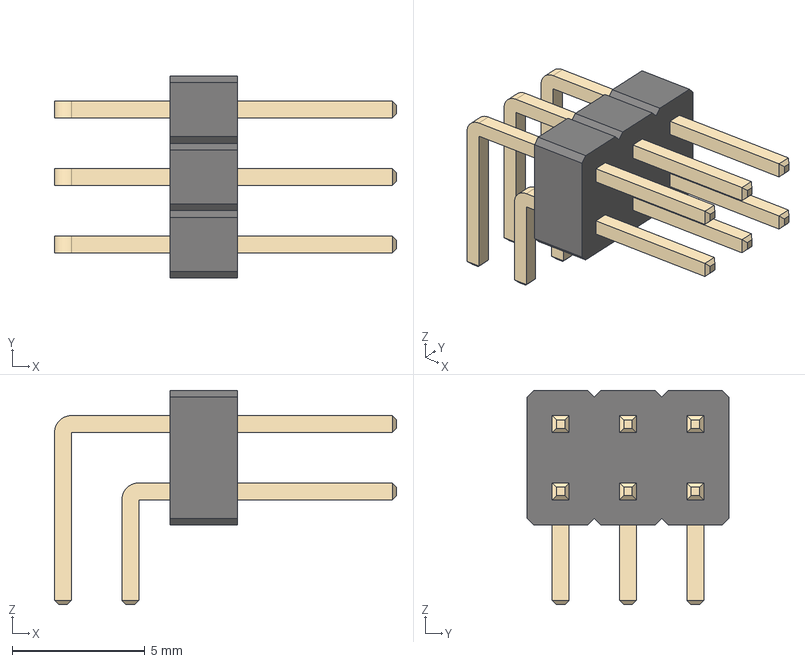
[picture p84: CAD file, 2026-03-01]
3d_models/PinHeader_2x03_P2.54mm_Horizontal.step
12.9 x 7.62 x 8.08 mm
