t-dsp/t-dsp_tac5212_audio_shield_adaptor/3d_models/SO-8_5.3x6.2mm_P1.27mm.step

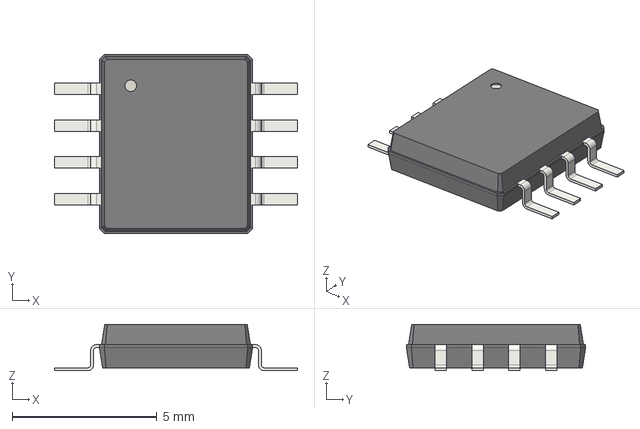
[picture p85: CAD file, 2026-03-01]
3d_models/SO-8_5.3x6.2mm_P1.27mm.step
8.40 x 6.20 x 1.60 mm
