t-dsp/t-dsp_tac5212_audio_shield_adaptor/3d_models/3-d-nmj6hcd3.stp

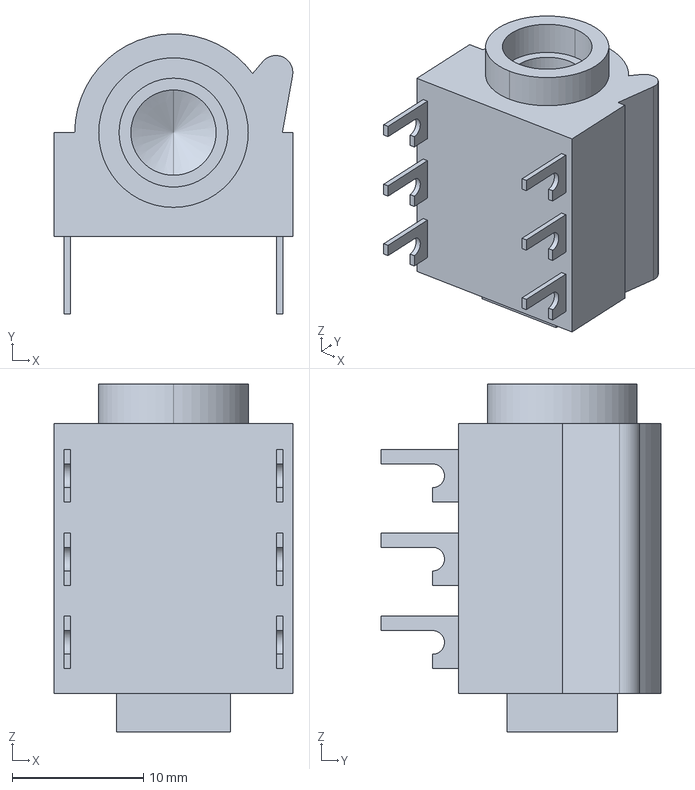
[picture p86: CAD file, 2026-03-01]
3d_models/3-d-nmj6hcd3.stp
18.2 x 21.4 x 26.5 mm
