t-dsp/t-dsp_tac5212_audio_shield_adaptor/3d_models/4691.step

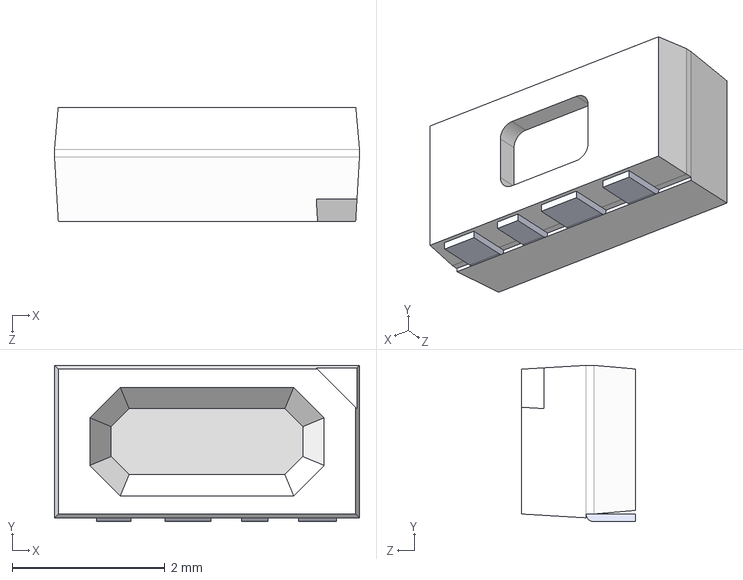
[picture p87: CAD file, 2026-03-01]
3d_models/4691.step
4.00 x 2.05 x 1.50 mm
