t-dsp/t-dsp_tac5212_audio_shield_adaptor/3d_models/TE_1775485-1_BATTERY.step

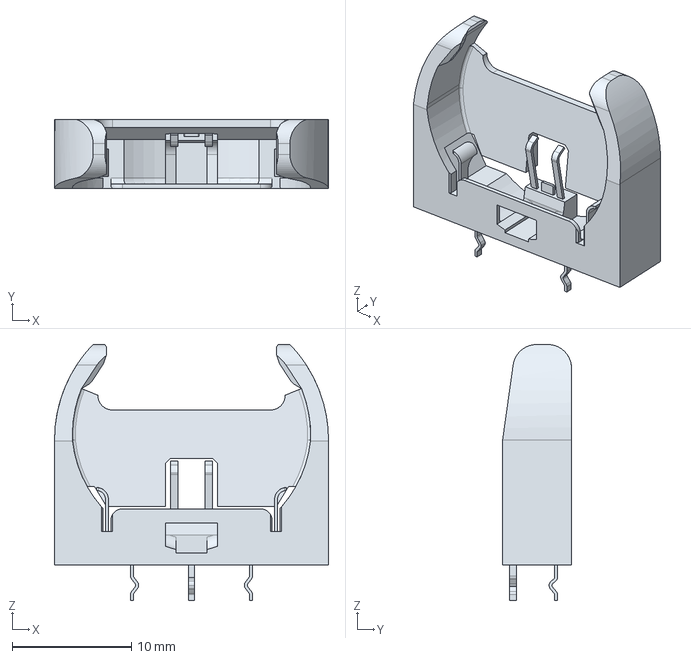
[picture p88: CAD file, 2026-03-01]
3d_models/TE_1775485-1_BATTERY.step
23.0 x 5.80 x 21.5 mm
